RoboTakao/NX15A/nx15a/Blynk/BLE.jpeg

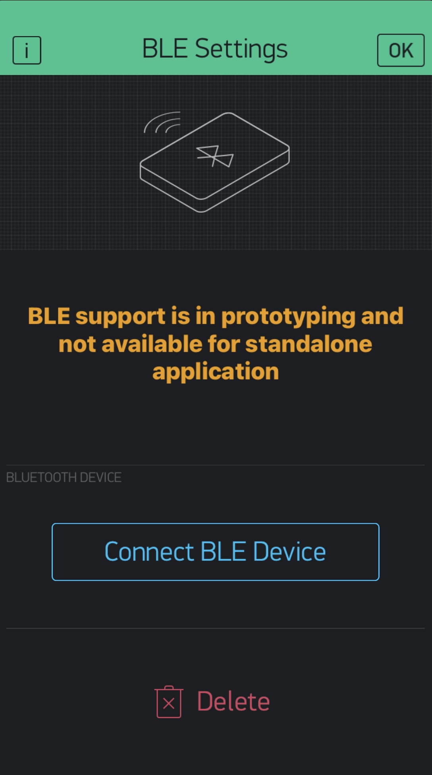
nx15a/Blynk/BLE.jpeg
