RoboTakao/NX15A/nx15a/STL_for_3Dprinting/Body_Cover02.stl

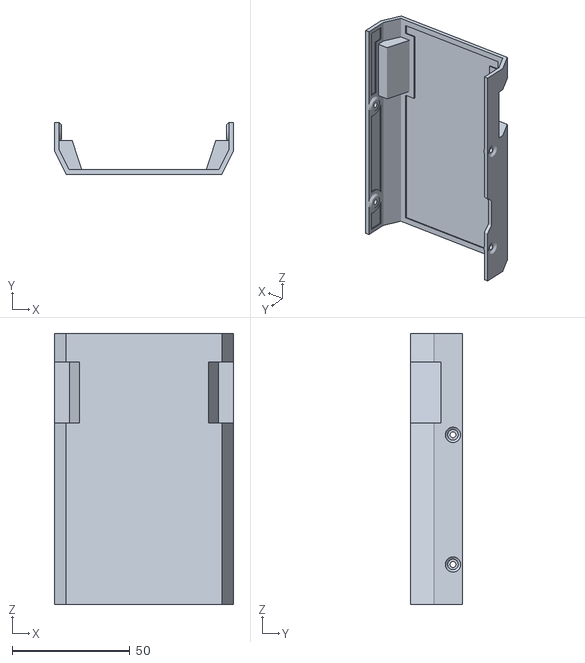
[picture p40: CAD file, 2021-05-23]
nx15a/STL_for_3Dprinting/Body_Cover02.stl
76.0 x 22.0 x 115.0
