RoboTakao/NX15A/nx15a/STL_for_3Dprinting/BoxRight.stl

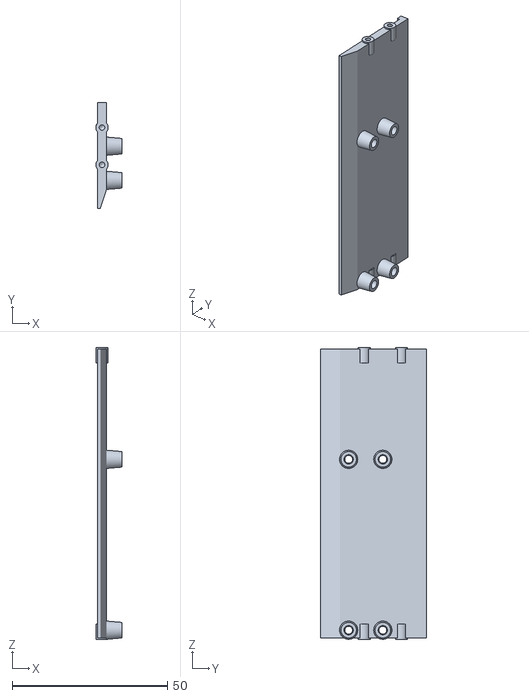
[picture p41: CAD file, 2021-05-23]
nx15a/STL_for_3Dprinting/BoxRight.stl
8.50 x 34.0 x 94.0
