RoboTakao/NX15A/nx15a/STL_for_3Dprinting/Stopper.stl

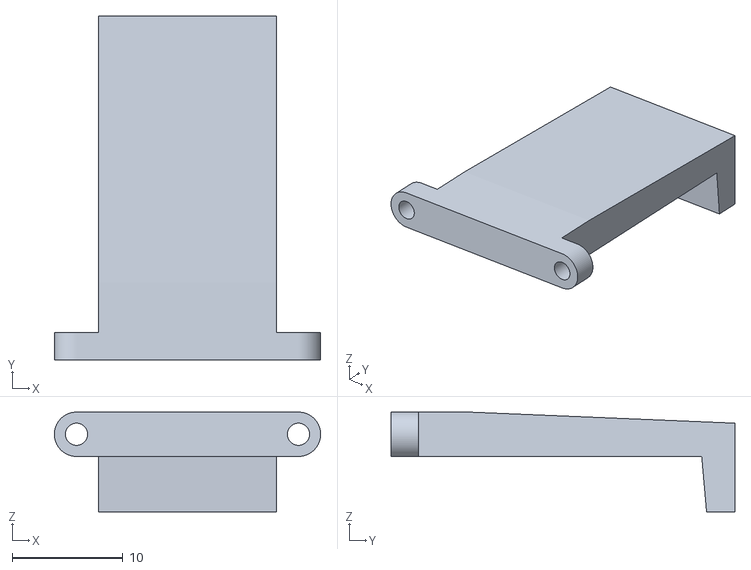
[picture p42: CAD file, 2021-05-23]
nx15a/STL_for_3Dprinting/Stopper.stl
24.0 x 31.0 x 9.00
