RoboTakao/NX15A/nx15a/STL_for_3Dprinting/Tail_Cover.stl

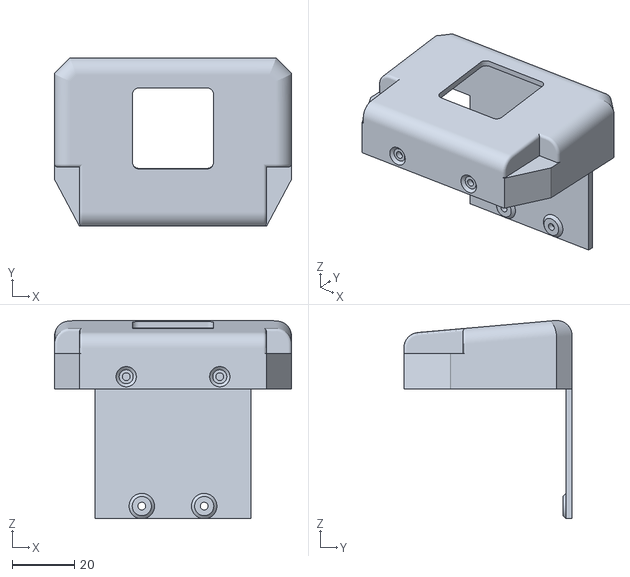
[picture p43: CAD file, 2021-05-23]
nx15a/STL_for_3Dprinting/Tail_Cover.stl
76.0 x 54.0 x 63.5
