RoboTakao/NX15A/nx15a/STL_for_3Dprinting/ServoBracket03.stl

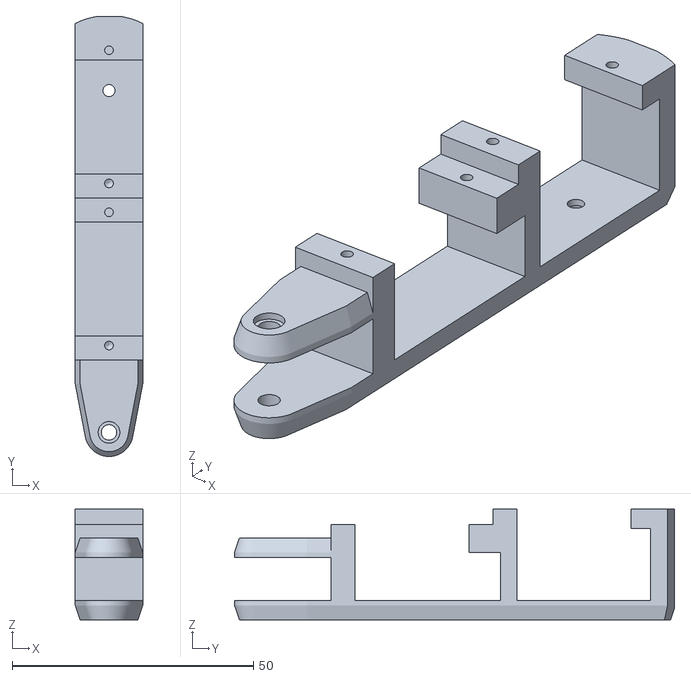
[picture p44: CAD file, 2021-05-23]
nx15a/STL_for_3Dprinting/ServoBracket03.stl
14.0 x 91.2 x 23.0
