RoboTakao/NX15A/nx15a/STL_for_3Dprinting/Lever.stl

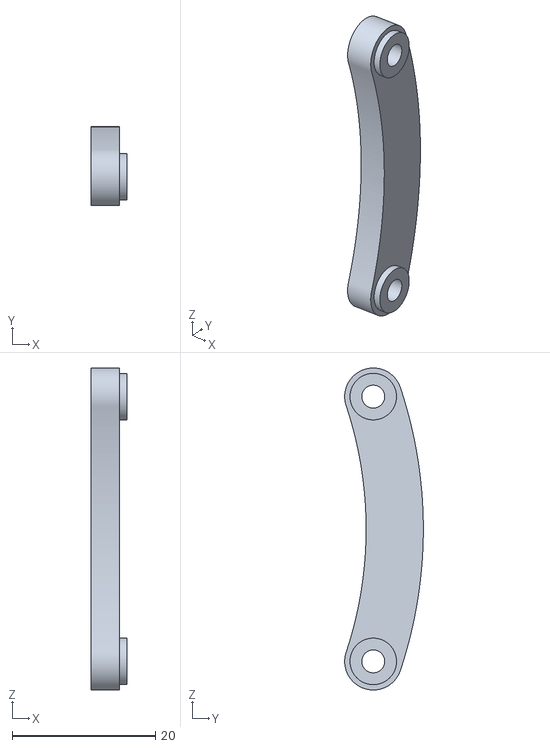
[picture p45: CAD file, 2021-05-23]
nx15a/STL_for_3Dprinting/Lever.stl
5.00 x 11.0 x 45.0
