RoboTakao/NX15A/nx15a/STL_for_3Dprinting/Head_Cover.stl

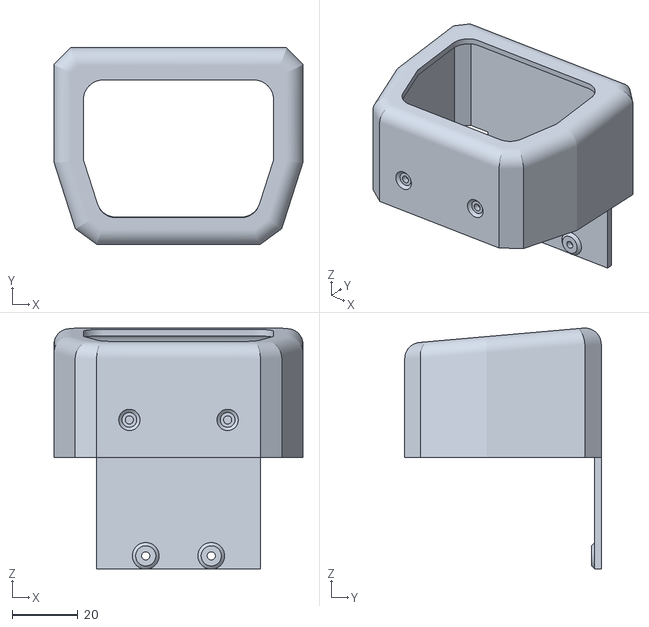
[picture p46: CAD file, 2021-05-23]
nx15a/STL_for_3Dprinting/Head_Cover.stl
76.0 x 60.0 x 73.5
