RoboTakao/NX15A/nx15a/STL_for_3Dprinting/Plate01.stl

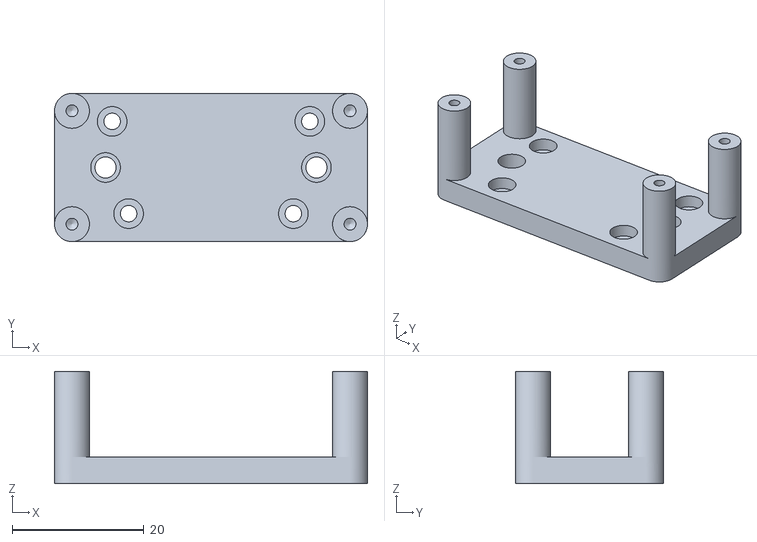
[picture p47: CAD file, 2021-05-23]
nx15a/STL_for_3Dprinting/Plate01.stl
47.5 x 22.5 x 17.0
